kruzpt/Build/designs/instagram-qr-stl-top.png

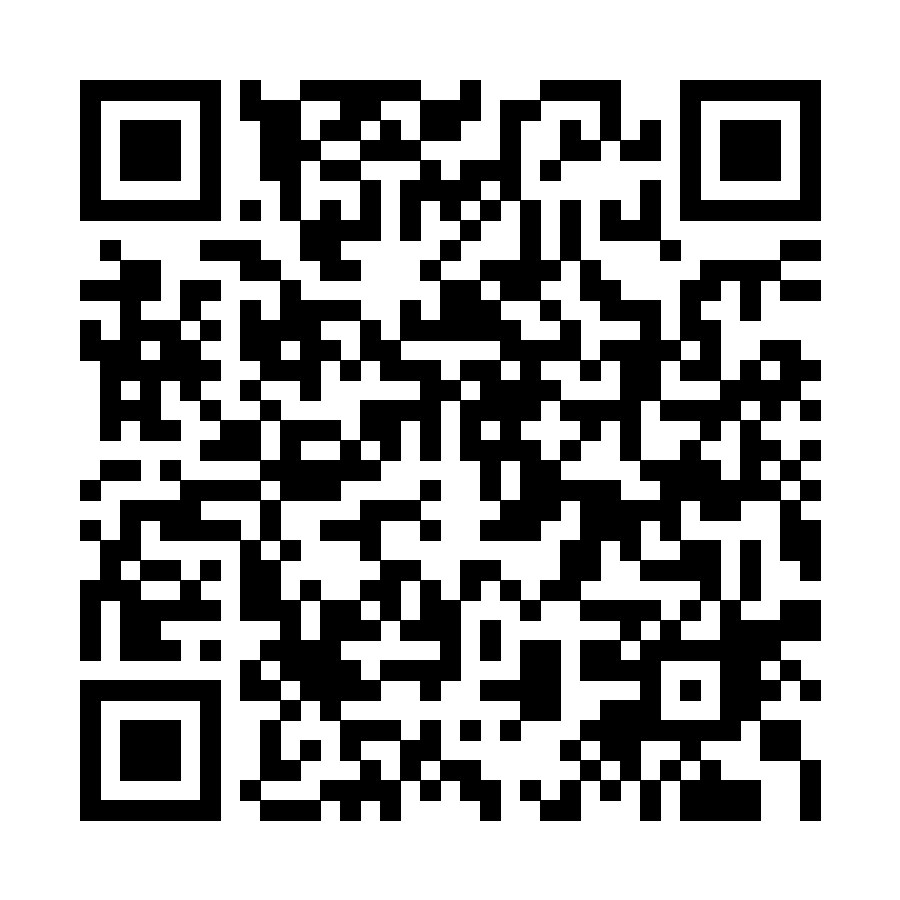
designs/instagram-qr-stl-top.png
