kruzpt/Build/designs/google-qr-test.png

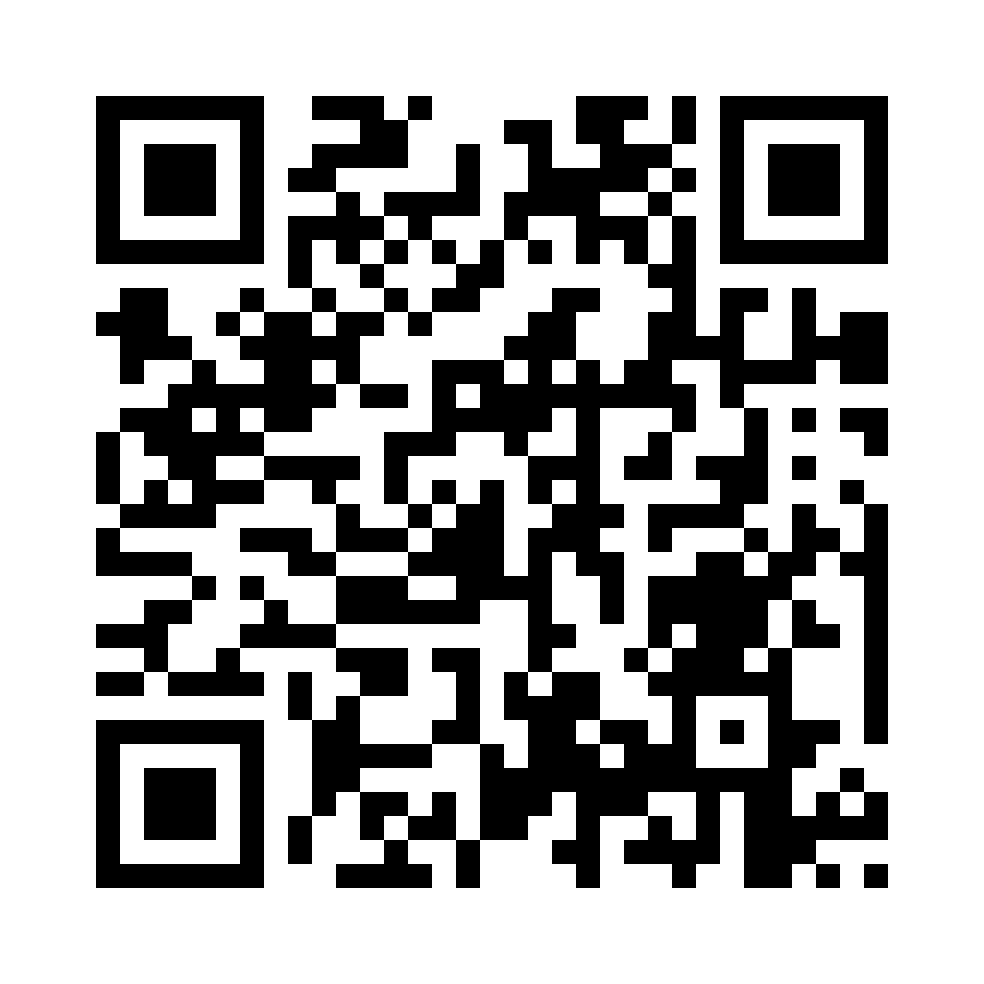
designs/google-qr-test.png
