kruzpt/Build/designs/google-reviews-qr-test.jpg

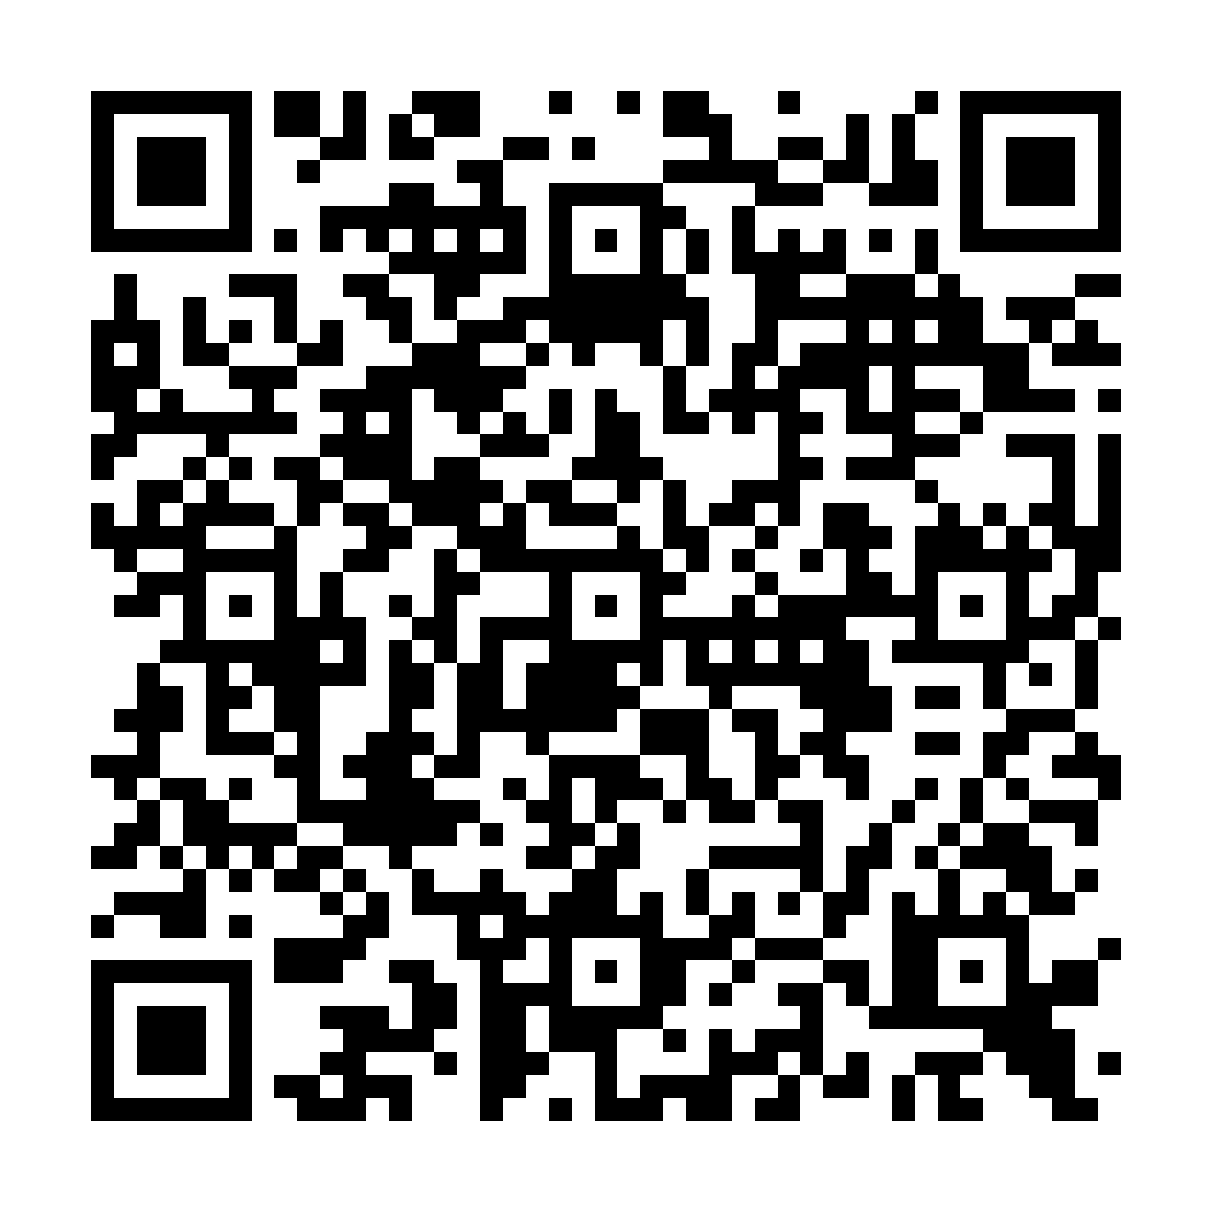
designs/google-reviews-qr-test.jpg
